scttnlsn/bms/src/bms.h

#ifndef __BMS_H__
#define __BMS_H__

#define BMS_NUM_CELLS 4
#define BMS_NOMINAL_CAPACITY 72000000 // mAs (20Ah)

int bms_init(void);
int bms_update(void);
uint8_t bms_status(void);
int bms_cell_voltages(uint16_t *voltages);
int16_t bms_current(void);
int32_t bms_charge(void);
uint8_t bms_soc(void);

#endif
