scttnlsn/bms/src/utils.c

#include "utils.h"

uint8_t crc8(const uint8_t *buffer, size_t length) {
  uint8_t crc = 0;

  for (int i = 0; i < length; i++) {
    uint8_t data = crc ^ buffer[i];

    for (int i = 0; i < 8; i++ ) {
      if (data & 0x80) {
        data <<= 1;
        data ^= 0x07;
      } else {
        data <<= 1;
      }
    }

    crc = data;
  }

  return crc;
}
